Andrei-Broscareanu/OpenBook-Reader/Images/Captură de ecran 2025-04-06 132220.png

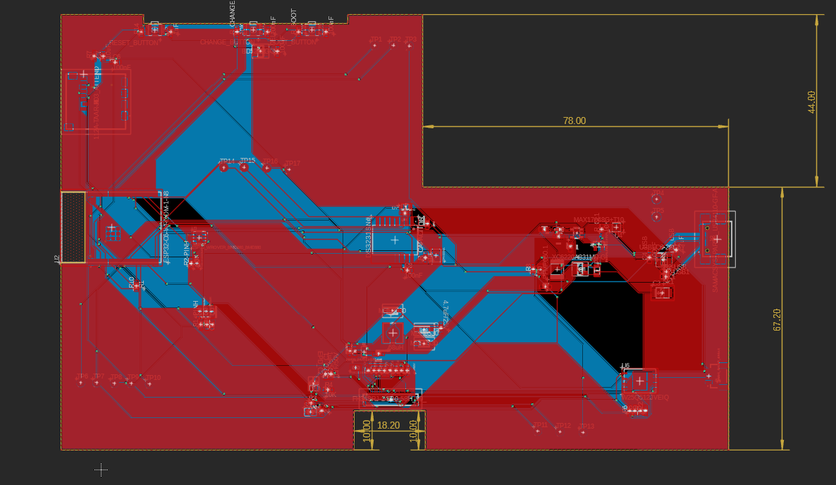
Images/Captură de ecran 2025-04-06 132220.png
